MarkJB/charliewatch/pcb/charliewatch-norf-routed.kicad_pcb

## KiCad design pcb/charliewatch-norf-routed.kicad_pcb (2019-09-23)

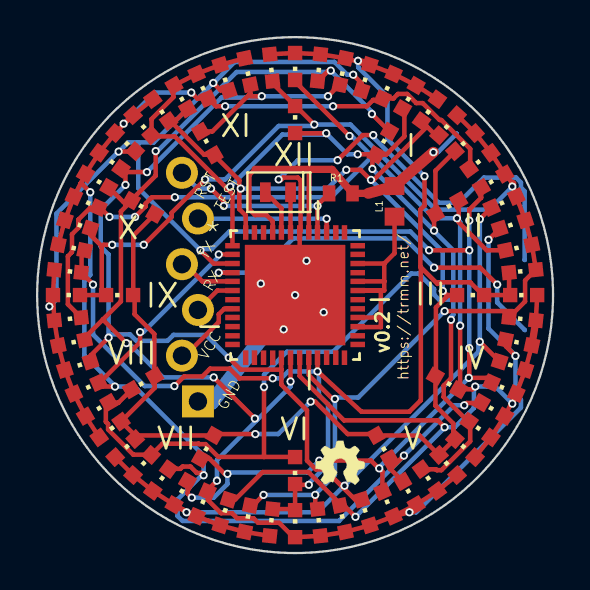
[picture p10: board charliewatch-norf-routed.kicad_pcb from above]

Board: 2 copper layers, 28.7 x 28.7 mm, 85 parts (0 on the bottom side), 20 nets.

Parts:
JP1: 1X06-BIGLOCK
L1: R0603
LED0, LED1, LED2, LED3, LED4, LED5, LED6, LED7, LED8, LED9, LED10, LED11, LED12, LED13, LED14, LED15, LED16, LED17, LED18, LED19, LED20, LED21, LED22, LED23, LED24, LED25, LED26, LED27, LED28, LED29, LED30, LED31, LED32, LED33, LED34, LED35, LED36, LED37, LED38, LED39, LED40, LED41, LED42, LED43, LED44, LED45, LED46, LED47, LED48, LED49, LED50, LED51, LED52, LED53, LED54, LED55, LED56, LED57, LED58, LED59, LED60, LED61, LED62, LED63, LED64, LED65, LED66, LED67, LED68, LED69, LED70, LED71: CHIPLED_0603
R1: 75k; R0402
S2: MOMENTARY-SWITCH-SPST-SMD-RIGHT-ANGLE; TACTILE_SWITCH_SMD_RIGHT_ANGLE
TP1: PTR1TP10SQ; TP10SQ
TP2, TP3, TP4, TP5, TP6: PTR1TP10R; TP10R
U2: CC430F5137IRGZR; QFN50P700X700X100-49N
U$1: CR2032-SMD
X1: CRYSTALS-NOGND-IQXC-25; 2.0X1.2-2PAD

Connections:
AVCC: L1.1, U2.27, U2.28, U2.31, U2.32, U2.34
B0: LED0.A, LED1.A, LED2.A, LED3.A, LED4.A, LED5.A, LED6.A, LED7.A, LED8.C, LED16.C, LED24.C, LED32.C, LED40.C, LED48.C, LED56.C, LED64.C, U2.21
B1: LED0.C, LED8.A, LED9.A, LED10.A, LED11.A, LED12.A, LED13.A, LED14.A, LED15.A, LED17.C, LED25.C, LED33.C, LED41.C, LED49.C, LED57.C, LED65.C, U2.20
B2: LED1.C, LED9.C, LED16.A, LED17.A, LED18.A, LED19.A, LED20.A, LED21.A, LED22.A, LED23.A, LED26.C, LED34.C, LED42.C, LED50.C, LED58.C, LED66.C, U2.19
B3: LED2.C, LED10.C, LED18.C, LED24.A, LED25.A, LED26.A, LED27.A, LED28.A, LED29.A, LED30.A, LED31.A, LED35.C, LED43.C, LED51.C, LED59.C, LED67.C, U2.18
B4: LED3.C, LED11.C, LED19.C, LED27.C, LED32.A, LED33.A, LED34.A, LED35.A, LED36.A, LED37.A, LED38.A, LED39.A, LED44.C, LED52.C, LED60.C, LED68.C, U2.17
B5: LED4.C, LED12.C, LED20.C, LED28.C, LED36.C, LED40.A, LED41.A, LED42.A, LED43.A, LED44.A, LED45.A, LED46.A, LED47.A, LED53.C, LED61.C, LED69.C, U2.3
B6: LED5.C, LED13.C, LED21.C, LED29.C, LED37.C, LED45.C, LED48.A, LED49.A, LED50.A, LED51.A, LED52.A, LED53.A, LED54.A, LED55.A, LED62.C, LED70.C, U2.2
B7: LED6.C, LED14.C, LED22.C, LED30.C, LED38.C, LED46.C, LED54.C, LED56.A, LED57.A, LED58.A, LED59.A, LED60.A, LED61.A, LED62.A, LED63.A, LED71.C, U2.1
B8: LED7.C, LED15.C, LED23.C, LED31.C, LED39.C, LED47.C, LED55.C, LED63.C, LED64.A, LED65.A, LED66.A, LED67.A, LED68.A, LED69.A, LED70.A, LED71.A, U2.48
BSL_RST: JP1.6, R1.1, TP6.TP, U2.40
BSL_RX: JP1.3, TP3.TP, U2.6
BSL_TEST: JP1.5, TP5.TP, U2.39
BSL_TX: JP1.4, TP4.TP, U2.5
BSL_VCC: JP1.2, TP2.TP, U2.8
BUTTON: S2.2, U2.4
GND: JP1.1, S2.1, TP1.TP, U2.42, U2.49, U$1.-
VCC: L1.2, R1.2, U2.41, U2.45, U$1.+$1
XIN: U2.44, X1.2
XOUT: U2.43, X1.1
